wleng2001/anesthesiological-cabinet/prowadnica/anc-1-0001-0003-0004-0004.SLDPRT

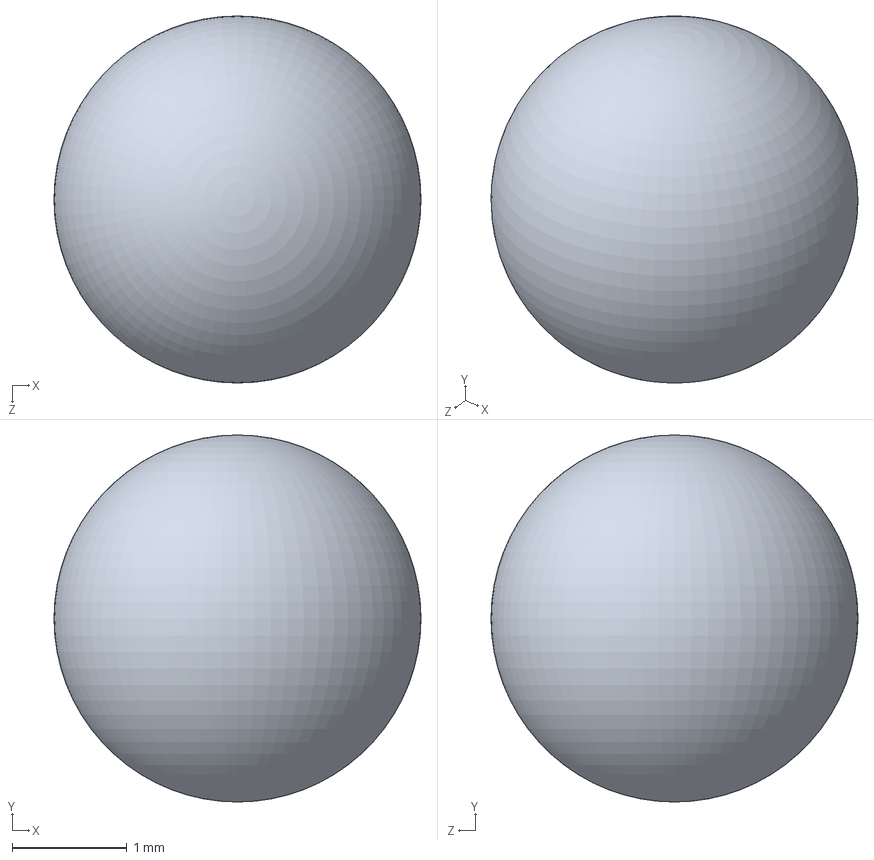
[picture p23: CAD file, 2023-01-18]
prowadnica/anc-1-0001-0003-0004-0004.SLDPRT
3.20 x 3.20 x 3.20 mm
