wleng2001/anesthesiological-cabinet/wieszak/anc-1-0001-0002-0001.SLDPRT

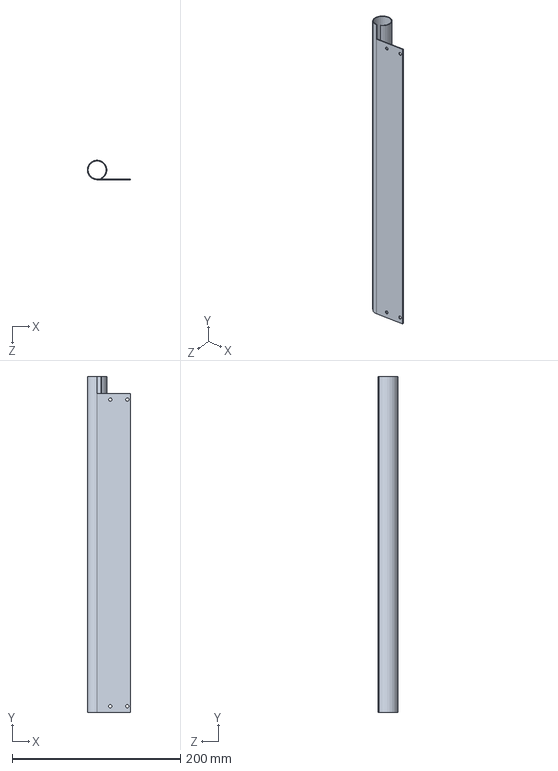
[picture p24: CAD file, 2023-01-18]
wieszak/anc-1-0001-0002-0001.SLDPRT
51.7 x 400.0 x 23.4 mm
