wleng2001/anesthesiological-cabinet/wózek/anc-1-0001-0001-0002.SLDPRT

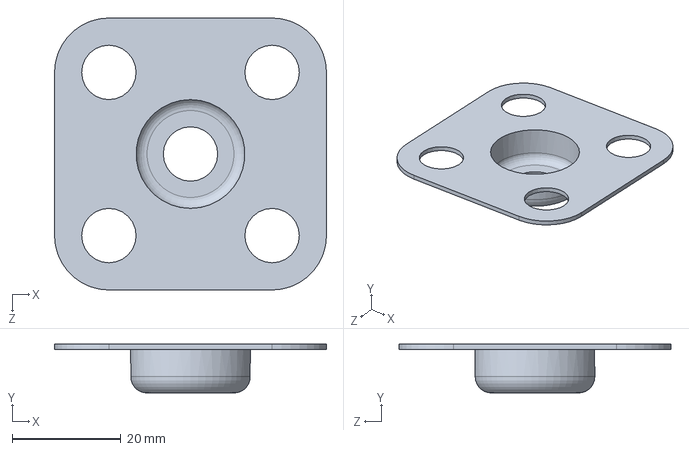
[picture p25: CAD file, 2023-01-19]
wózek/anc-1-0001-0001-0002.SLDPRT
50.0 x 9.00 x 50.0 mm
