wleng2001/anesthesiological-cabinet/anc-1-0001-0007.SLDPRT

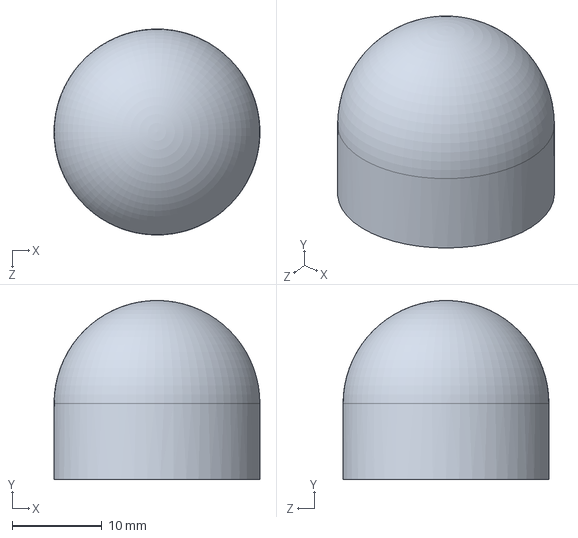
[picture p26: CAD file, 2023-03-10]
anc-1-0001-0007.SLDPRT
23.0 x 20.0 x 23.0 mm
