wleng2001/anesthesiological-cabinet/prowadnica/anc-1-0001-0003-0004-0002.SLDPRT

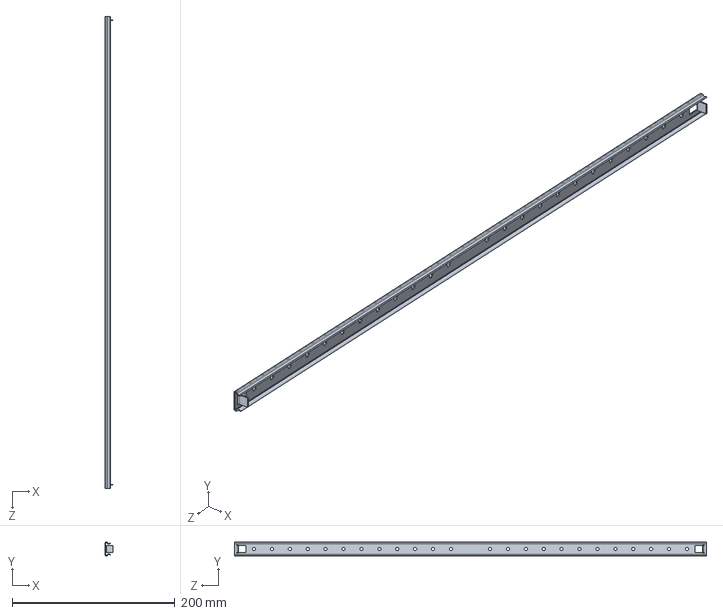
[picture p27: CAD file, 2023-01-18]
prowadnica/anc-1-0001-0003-0004-0002.SLDPRT
10.0 x 17.0 x 580.0 mm
