wleng2001/anesthesiological-cabinet/wieszak/anc-1-0001-0001-0002-0004.SLDPRT

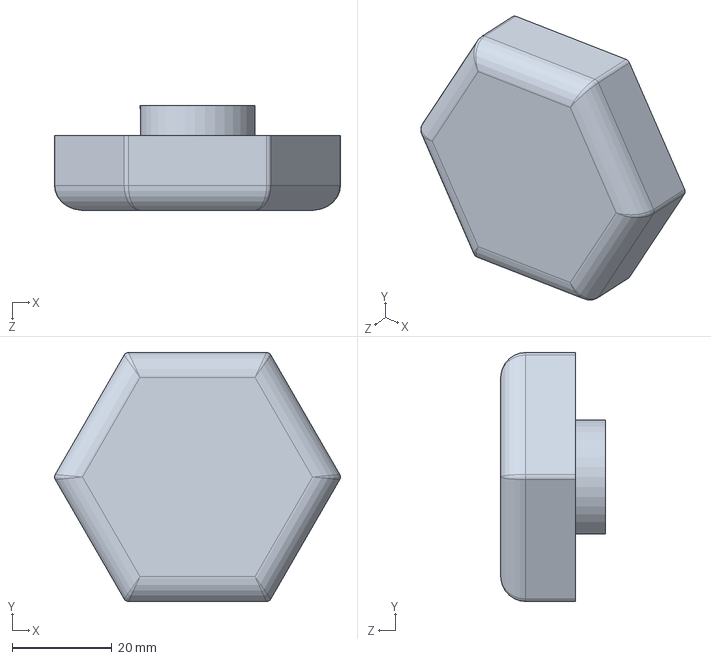
[picture p28: CAD file, 2023-01-18]
wieszak/anc-1-0001-0001-0002-0004.SLDPRT
57.4 x 50.0 x 21.0 mm
