wleng2001/anesthesiological-cabinet/wózek/anc-1-0001-0001-0001-0007.SLDPRT

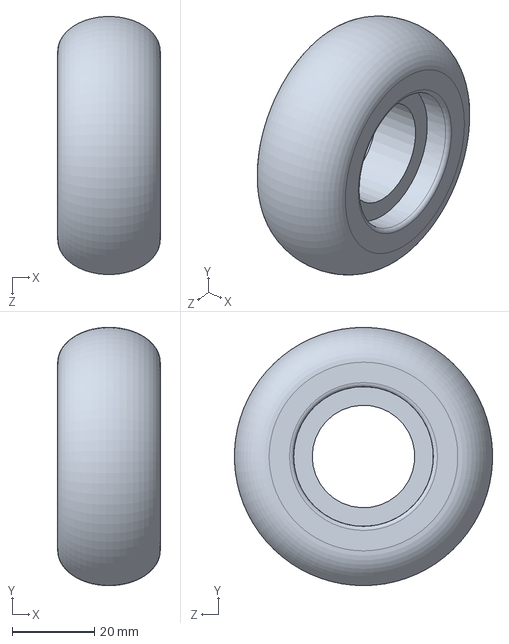
[picture p29: CAD file, 2023-01-19]
wózek/anc-1-0001-0001-0001-0007.SLDPRT
25.0 x 63.0 x 62.9 mm
