wleng2001/anesthesiological-cabinet/anc-1-0001-0005.SLDPRT

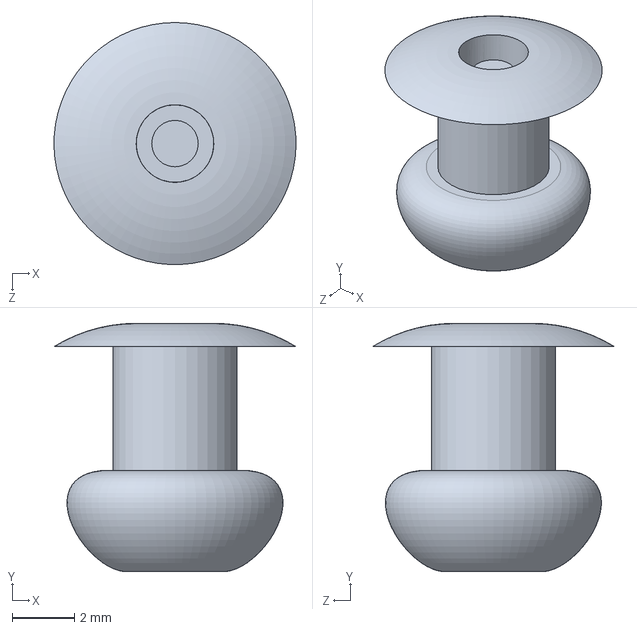
[picture p30: CAD file, 2023-03-10]
anc-1-0001-0005.SLDPRT
7.80 x 8.00 x 7.80 mm
