wleng2001/anesthesiological-cabinet/prowadnica/forma ograniczenia wysuwu.SLDPRT

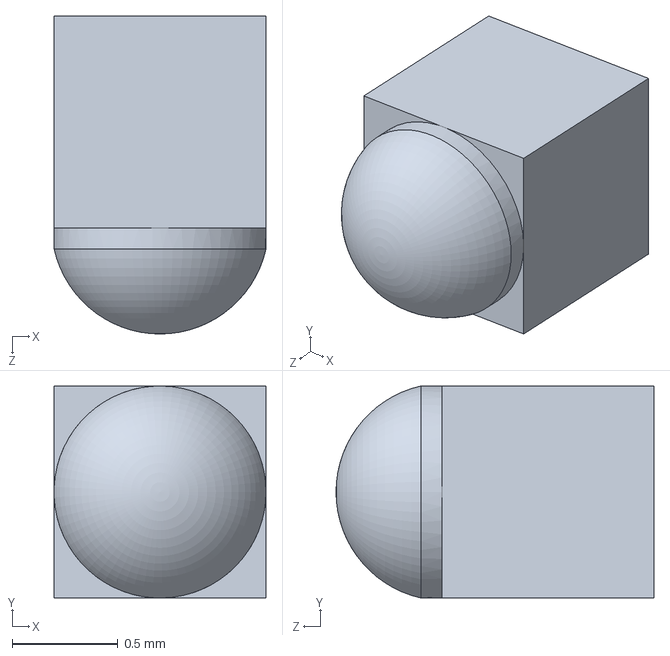
[picture p31: CAD file, 2022-12-17]
prowadnica/forma ograniczenia wysuwu.SLDPRT
1.00 x 1.00 x 1.50 mm
