wleng2001/anesthesiological-cabinet/wózek/circlip for bores normal_din.SLDPRT

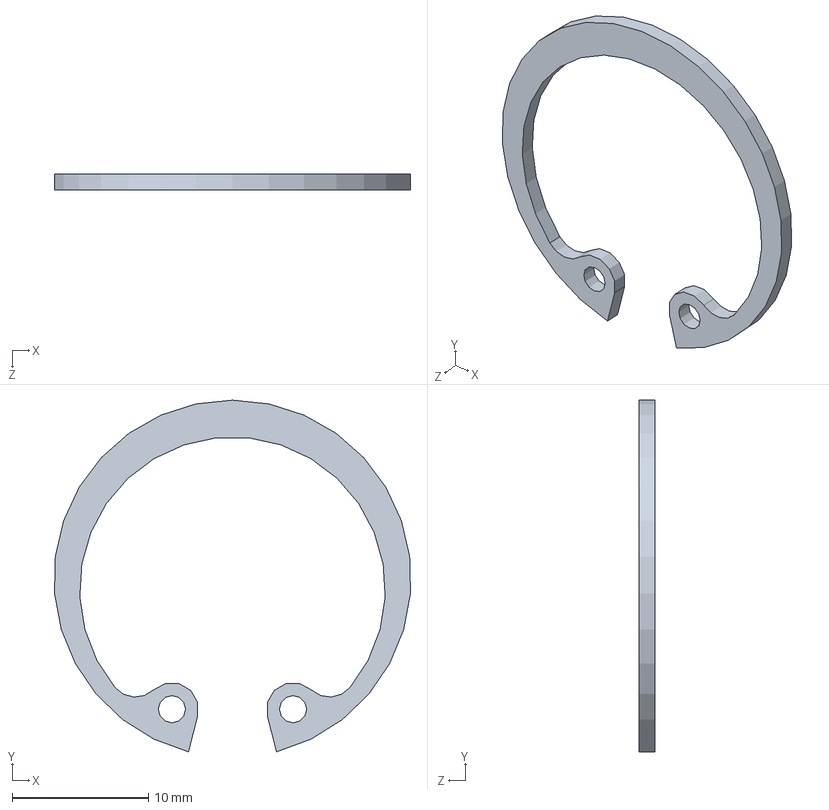
[picture p32: CAD file, 2023-01-19]
wózek/circlip for bores normal_din.SLDPRT
26.1 x 25.8 x 1.20 mm
