wleng2001/anesthesiological-cabinet/anc-1-0001-0003-0002.SLDPRT

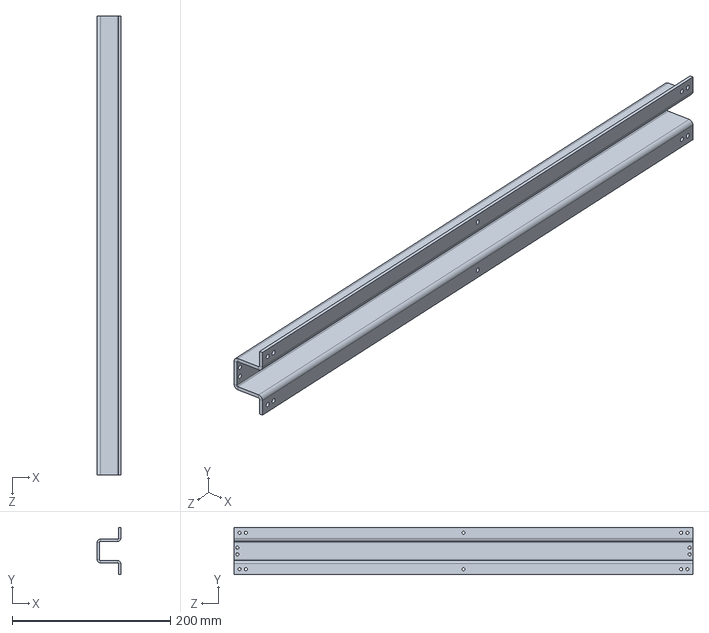
[picture p33: CAD file, 2023-01-27]
anc-1-0001-0003-0002.SLDPRT
30.0 x 60.0 x 580.0 mm
