wleng2001/anesthesiological-cabinet/wózek/łożysko/anc-1-0001-0001-0001-0001.SLDPRT

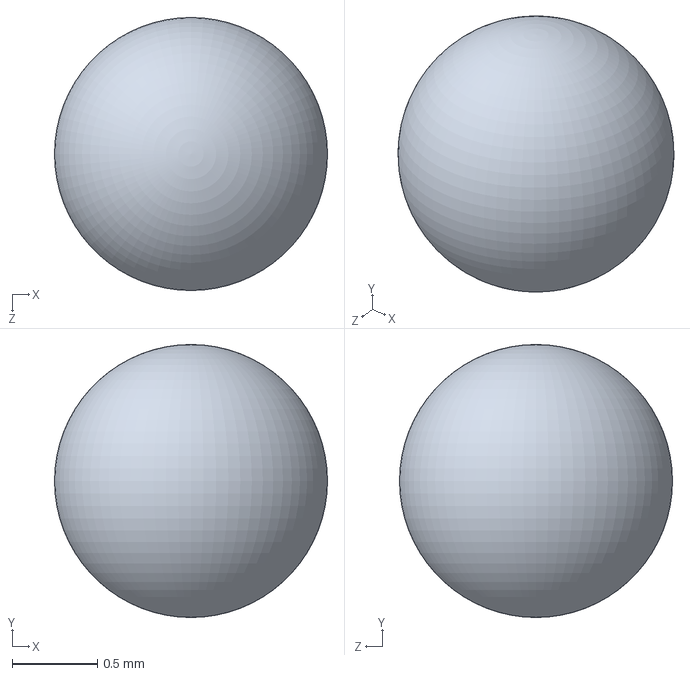
[picture p34: CAD file, 2023-01-18]
wózek/łożysko/anc-1-0001-0001-0001-0001.SLDPRT
1.60 x 1.60 x 1.60 mm
