wleng2001/anesthesiological-cabinet/anc-1-0001-0003-0003.SLDPRT

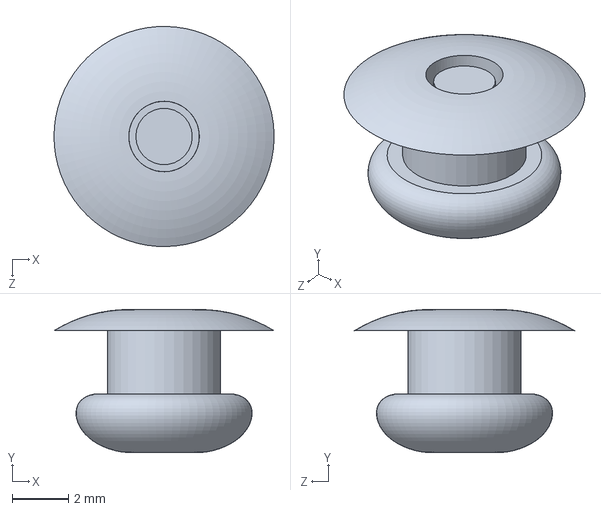
[picture p35: CAD file, 2023-01-27]
anc-1-0001-0003-0003.SLDPRT
7.80 x 5.07 x 7.80 mm
