wleng2001/anesthesiological-cabinet/wózek/anc-1-0001-0001-0004.SLDPRT

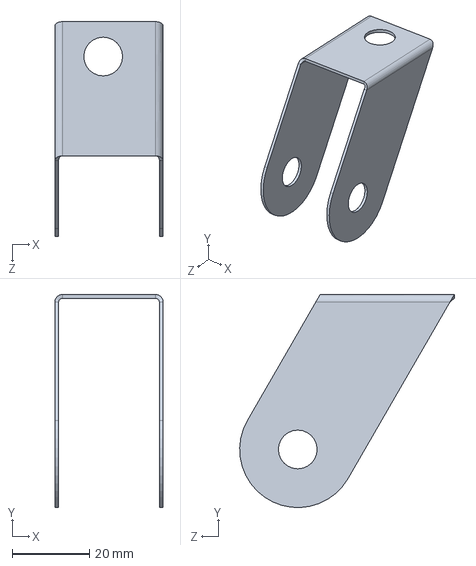
[picture p36: CAD file, 2023-01-19]
wózek/anc-1-0001-0001-0004.SLDPRT
28.0 x 55.0 x 55.4 mm
