wleng2001/anesthesiological-cabinet/wózek/łożysko/anc-1-0001-0001-0001-0002.SLDPRT

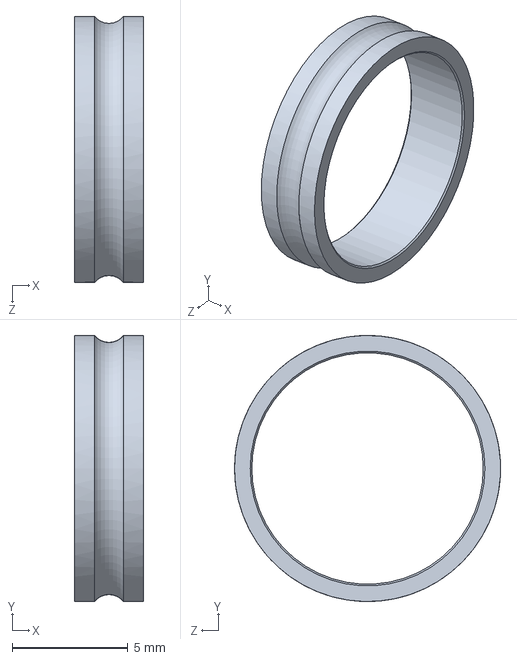
[picture p37: CAD file, 2023-01-18]
wózek/łożysko/anc-1-0001-0001-0001-0002.SLDPRT
3.00 x 11.5 x 11.5 mm
