wleng2001/anesthesiological-cabinet/anc-1-0001-0003-0001.SLDPRT

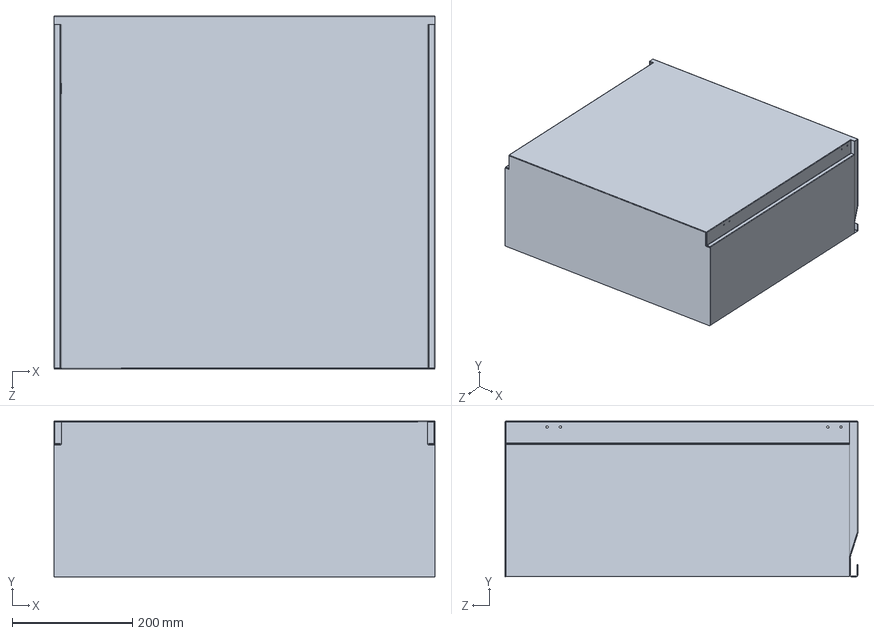
[picture p38: CAD file, 2023-01-27]
anc-1-0001-0003-0001.SLDPRT
632.6 x 259.0 x 586.0 mm
