wleng2001/anesthesiological-cabinet/wózek/łożysko/łożysko złożenie.SLDPRT

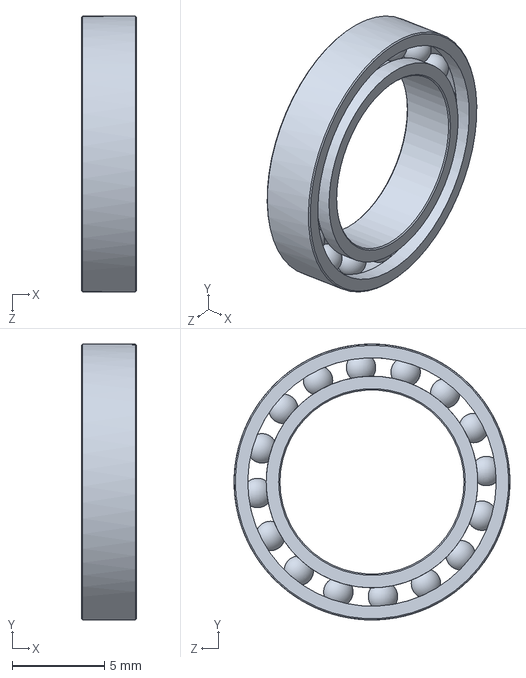
[picture p39: CAD file, 2022-12-19]
wózek/łożysko/łożysko złożenie.SLDPRT
3.00 x 15.0 x 15.0 mm
