wleng2001/anesthesiological-cabinet/nit zużyty.SLDPRT

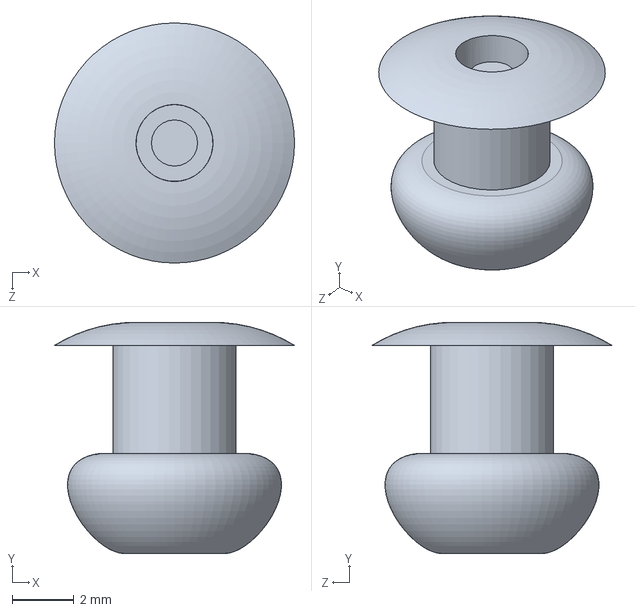
[picture p40: CAD file, 2023-01-24]
nit zużyty.SLDPRT
7.80 x 7.52 x 7.80 mm
