wleng2001/anesthesiological-cabinet/nit.SLDPRT

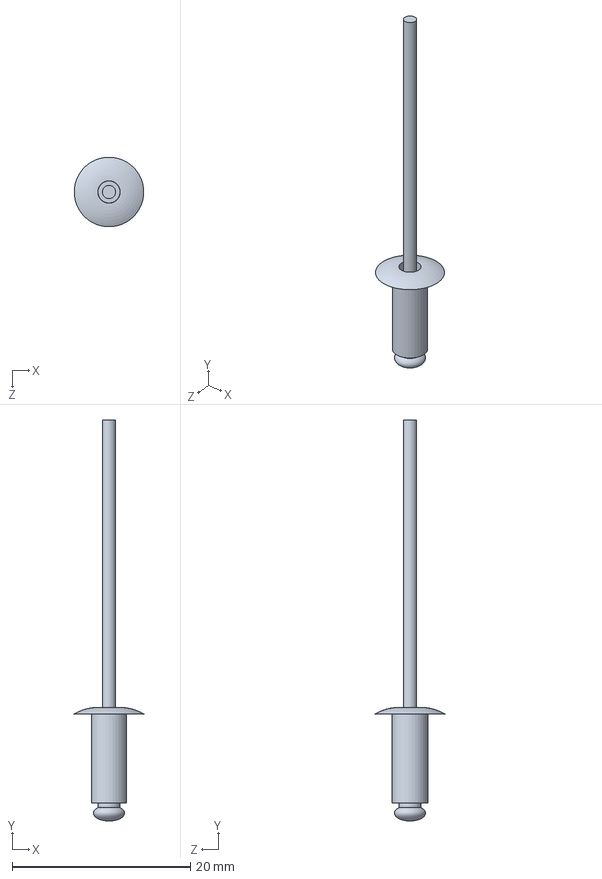
[picture p41: CAD file, 2023-01-12]
nit.SLDPRT
7.79 x 45.0 x 7.80 mm
