wleng2001/anesthesiological-cabinet/wózek/anc-1-0001-0001-0003.SLDPRT

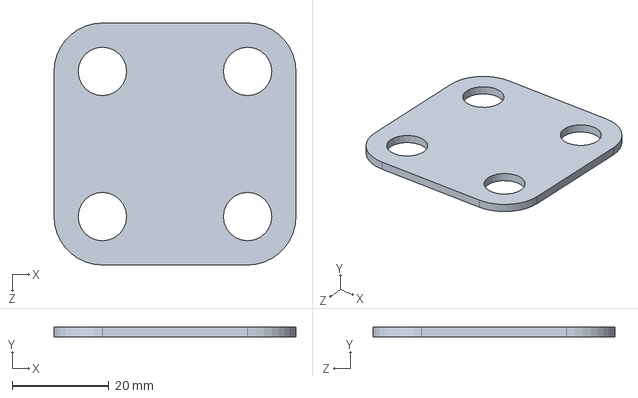
[picture p42: CAD file, 2023-01-18]
wózek/anc-1-0001-0001-0003.SLDPRT
50.0 x 2.00 x 50.0 mm
