wleng2001/anesthesiological-cabinet/wózek/narzędzie do formowania.SLDPRT

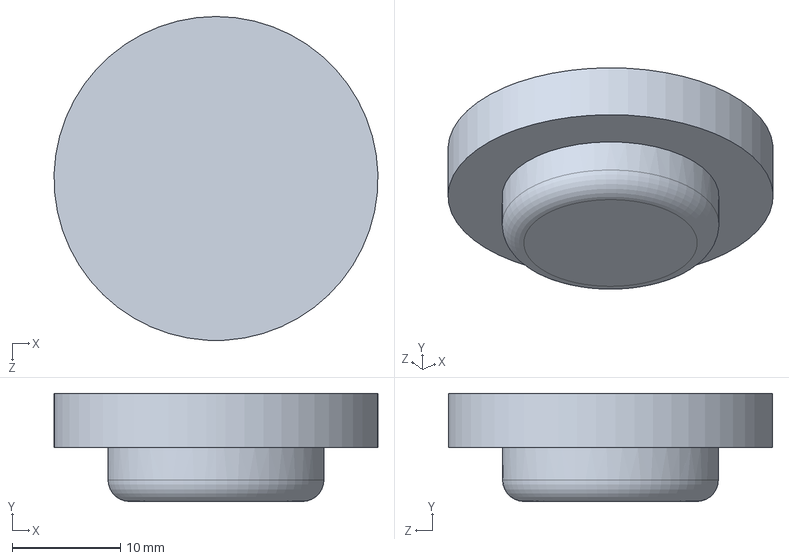
[picture p43: CAD file, 2022-12-17]
wózek/narzędzie do formowania.SLDPRT
30.0 x 10.0 x 30.0 mm
